abel3032/Voltage-Regulator/Simulations/Amplificare_bucla_deschisa.jpg

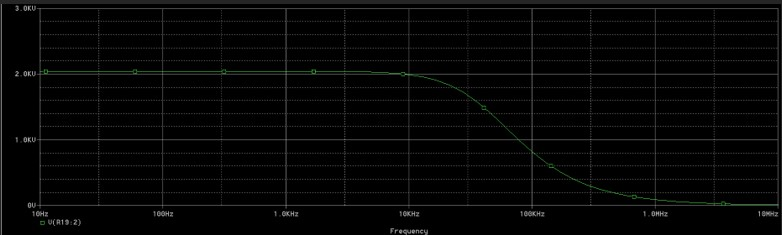
Simulations/Amplificare_bucla_deschisa.jpg
