abel3032/Voltage-Regulator/Simulations/Deriva_termica.jpg

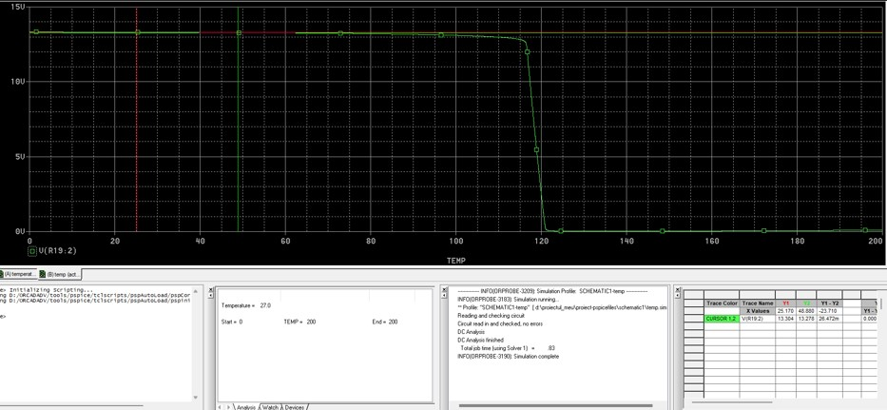
Simulations/Deriva_termica.jpg
