abel3032/Voltage-Regulator/Simulations/Protectie_suprasarcina.jpg

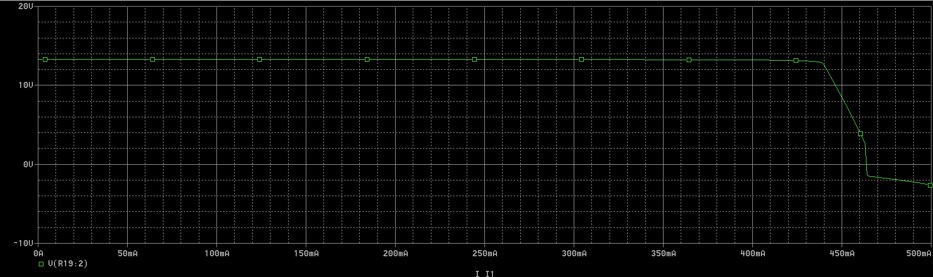
Simulations/Protectie_suprasarcina.jpg
