abel3032/Voltage-Regulator/Simulations/Vout_minim_interval_0_60.jpg

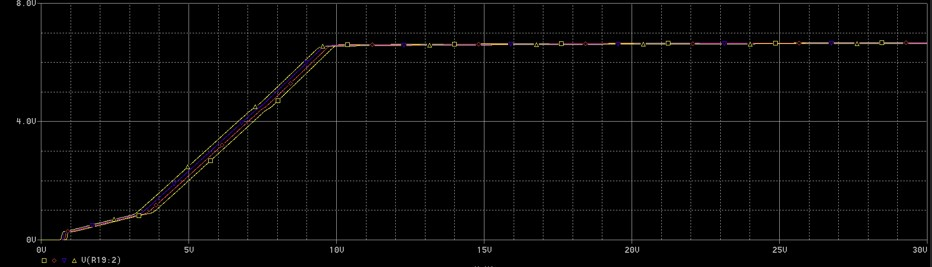
Simulations/Vout_minim_interval_0_60.jpg
